SunboX/Rotary-Dial-Tester-Adapter/pictures/setup-rotary-dial-and-adapter-portrait.jpg

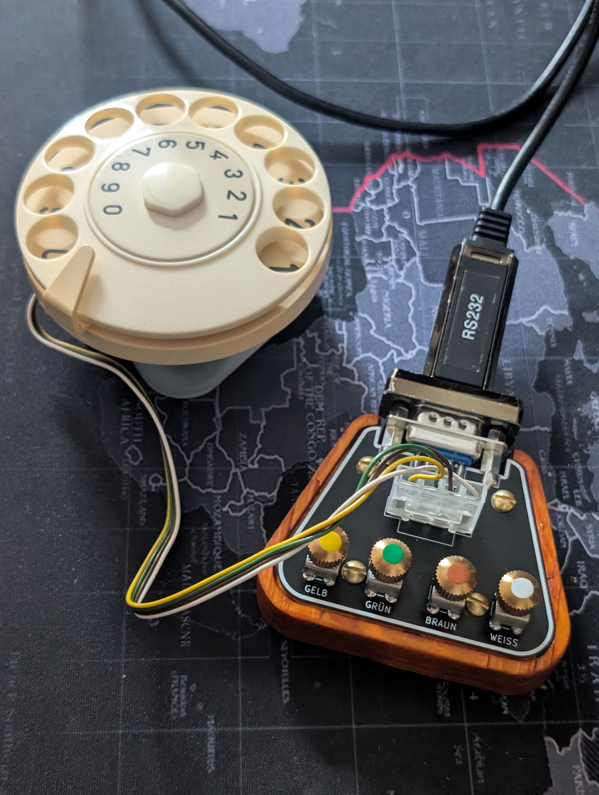
pictures/setup-rotary-dial-and-adapter-portrait.jpg
