SunboX/Rotary-Dial-Tester-Adapter/pictures/setup-rotary-dial-and-adapter-wide.jpg

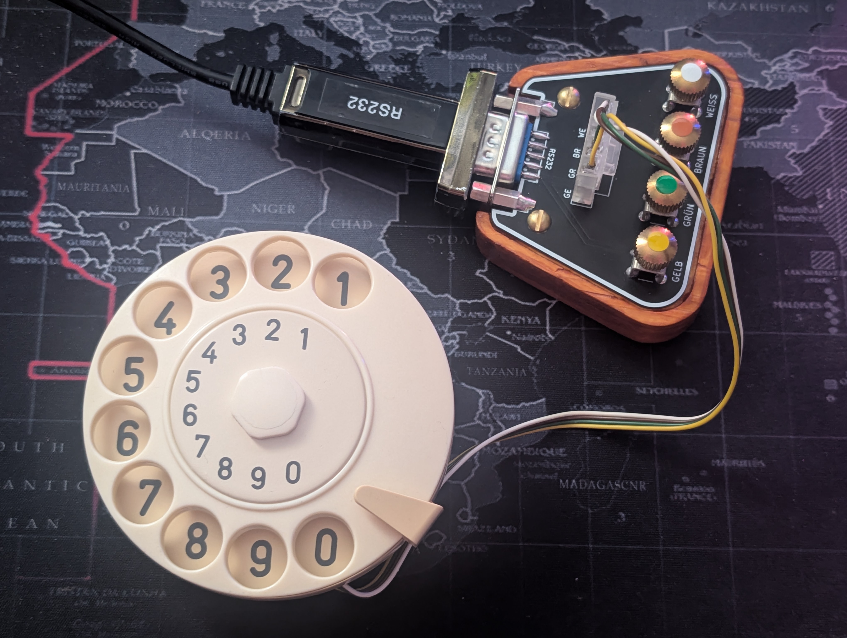
pictures/setup-rotary-dial-and-adapter-wide.jpg
